brucemack/kc1fsz-tjdcr/docs/2025-02-23_16-26-16.png

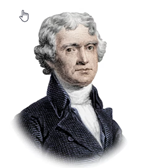
docs/2025-02-23_16-26-16.png
